GreenMashedPotato/Shrimp42/Case/Rev2/Acrylic Case/individual/second left 4mm.dxf

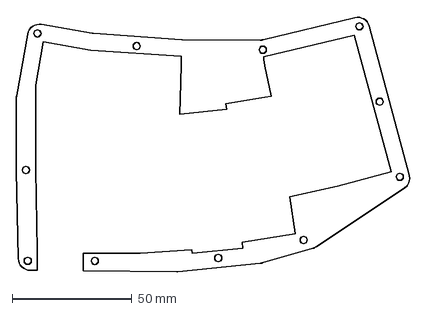
[picture p25: CAD file, 2022-08-07]
Case/Rev2/Acrylic Case/individual/second left 4mm.dxf
164.7 x 106.8 mm
