GreenMashedPotato/Shrimp42/Case/Rev2/Acrylic Case/individual/middle right 2 4mm.dxf

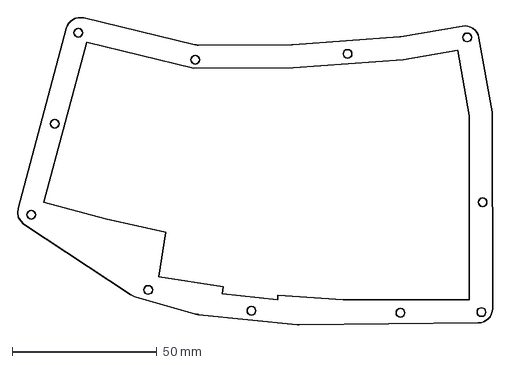
[picture p26: CAD file, 2022-08-07]
Case/Rev2/Acrylic Case/individual/middle right 2 4mm.dxf
164.7 x 106.8 mm
