GreenMashedPotato/Shrimp42/Rev1/Mirrored Rev1/kibod-01-mirrored.step

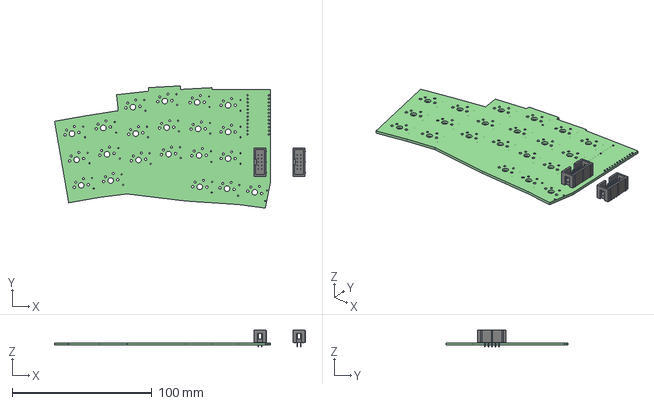
[picture p27: CAD file, 2022-01-05, an earlier design]
Rev1/Mirrored Rev1/kibod-01-mirrored.step
179.9 x 87.6 x 12.1 mm
